jamesorry/RP2040_LCD_16KeyPad/firmware/images/697476.bmp

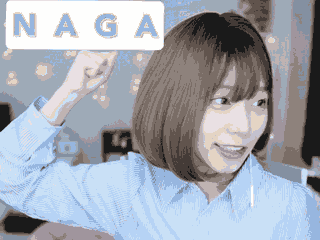
firmware/images/697476.bmp
