jamesorry/RP2040_LCD_16KeyPad/firmware/images/LINE_ALBUM_2022517_220517_0.bmp

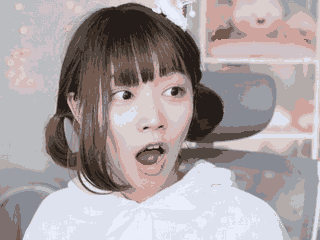
firmware/images/LINE_ALBUM_2022517_220517_0.bmp
