jamesorry/RP2040_LCD_16KeyPad/firmware/images/lisa_3.bmp

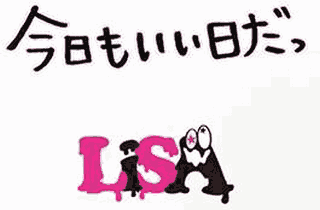
firmware/images/lisa_3.bmp
