jamesorry/RP2040_LCD_16KeyPad/images/Bottom_Holder.png

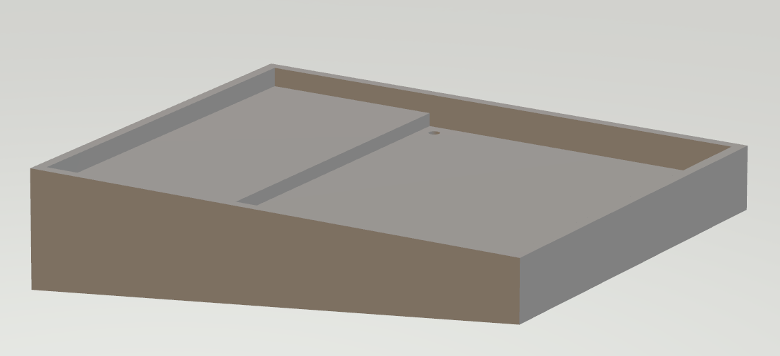
images/Bottom_Holder.png
